albkirk/MoodLight/Media/3D View.png

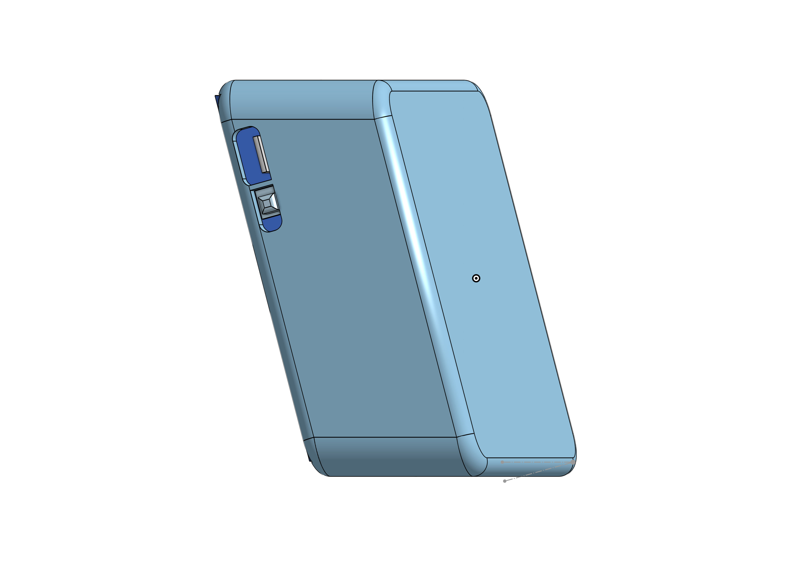
Media/3D View.png
